potblitd/DigiLog-Clock/images/00.JPG

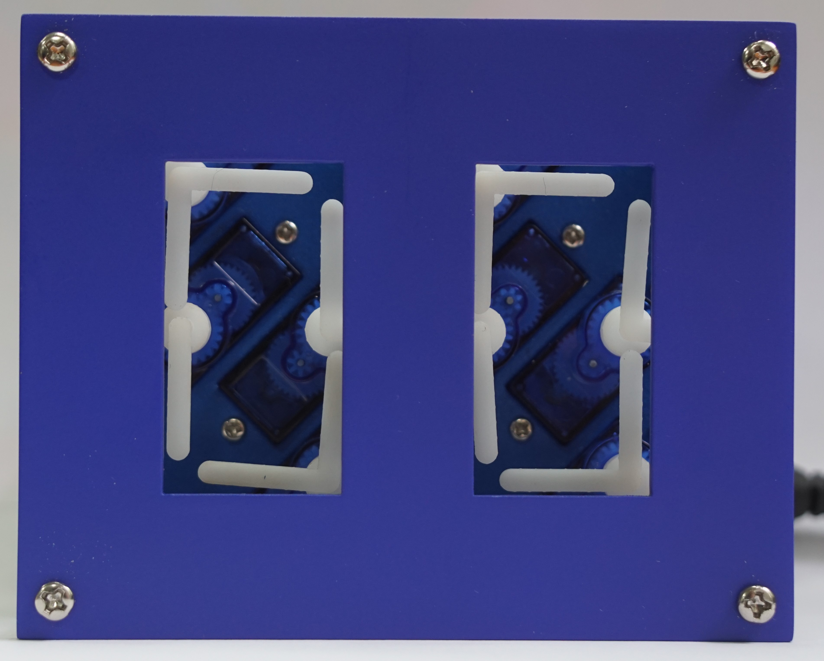
images/00.JPG
